CarAI-FIAP/PCB/Renders/V3/1.png

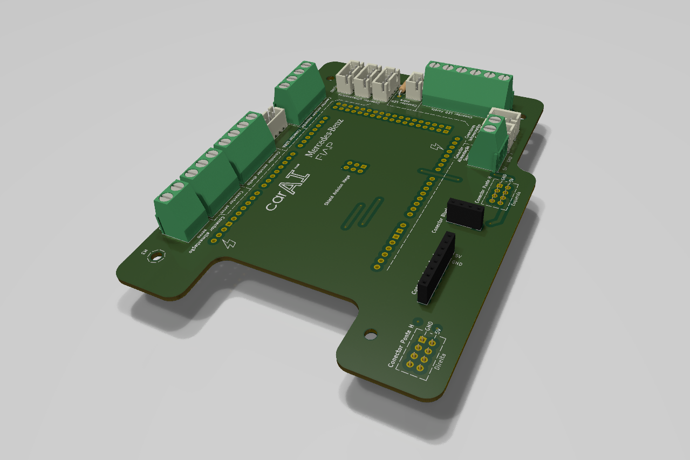
Renders/V3/1.png
