CarAI-FIAP/PCB/Renders/V3/2.png

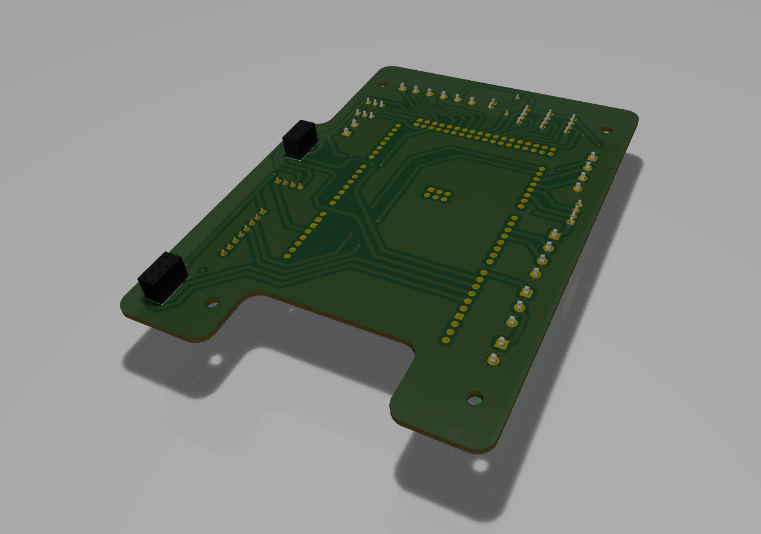
Renders/V3/2.png
