CarAI-FIAP/PCB/Renders/V3/3.png

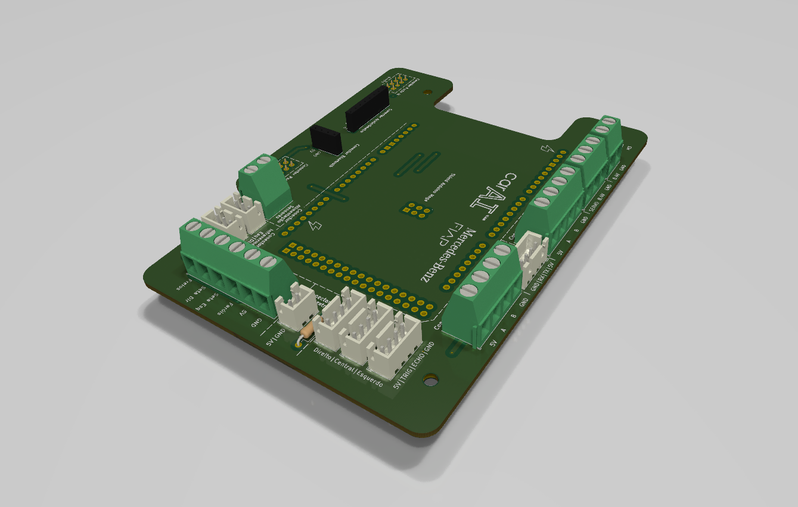
Renders/V3/3.png
